JayesonLS/SmartWatchRedux/SmartWatchTest/SmartWatchTest.kicad_pcb

## KiCad design Schematic/RPN-Calculator/RPN-Calculator.sch

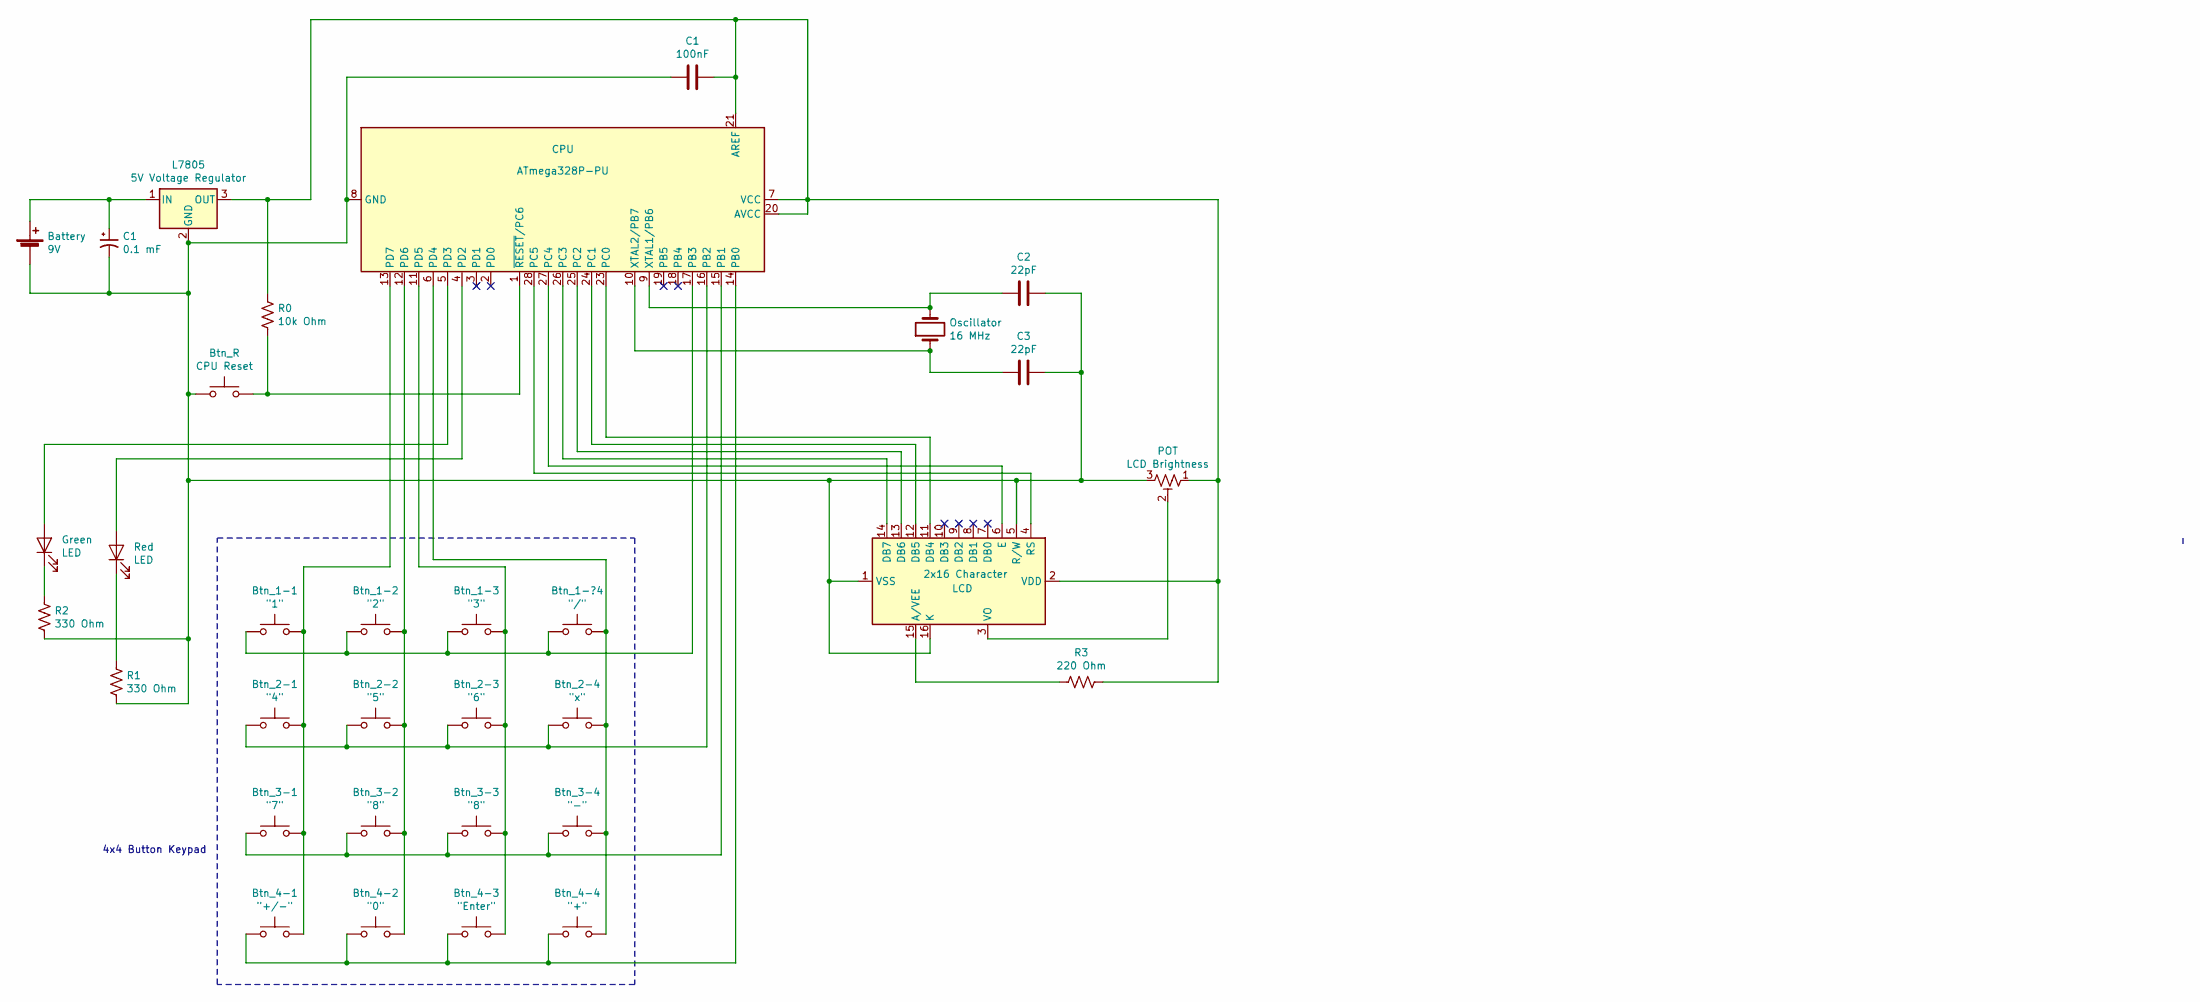
[picture p2: schematic RPN-Calculator.sch]

Parts:
Battery: 9V
Btn_1-1: \"1\"
Btn_1-2: \"2\"
Btn_1-3: \"3\"
Btn_1-?4: \"/\"
Btn_2-1: \"4\"
Btn_2-2: \"5\"
Btn_2-3: \"6\"
Btn_2-4: \"x\"
Btn_3-1: \"7\"
Btn_3-2, Btn_3-3: \"8\"
Btn_3-4: \"-\"
Btn_4-1: \"+/-\"
Btn_4-2: \"0\"
Btn_4-3: \"Enter\"
Btn_4-4: \"+\"
Btn_R: CPU Reset
C1: 100nF
C2, C3: 22pF
CPU: ATmega328P-PU; DIP-28_W7.62mm
Green: LED
L7805: 5V Voltage Regulator
LCD: 2x16 Character; RC1602A
Oscillator: 16 MHz
POT: LCD Brightness
R0: 10k Ohm
R1, R2: 330 Ohm
R3: 220 Ohm
Red: LED

Connections:
unnamed: Battery.1 (+), C1.1, L7805.1 (IN)
unnamed: Battery.2 (-), Btn_R.1, C1.2, C2.2, C3.2, CPU.8 (GND), CPU.22 (GND), L7805.2 (GND), LCD.1 (VSS), LCD.5 (R/W), LCD.16 (K), POT.3, R1.2, R2.2
unnamed: Btn_1-1.1, Btn_1-2.1, Btn_1-3.1, Btn_1-?4.1, CPU.17 (PB3)
unnamed: Btn_1-1.2, Btn_2-1.2, Btn_3-1.2, Btn_4-1.2, CPU.13 (PD7)
unnamed: Btn_1-2.2, Btn_2-2.2, Btn_3-2.2, Btn_4-2.2, CPU.12 (PD6)
unnamed: Btn_1-3.2, Btn_2-3.2, Btn_3-3.2, Btn_4-3.2, CPU.11 (PD5)
unnamed: Btn_1-?4.2, Btn_2-4.2, Btn_3-4.2, Btn_4-4.2, CPU.6 (PD4)
unnamed: Btn_2-1.1, Btn_2-2.1, Btn_2-3.1, Btn_2-4.1, CPU.16 (PB2)
unnamed: Btn_3-1.1, Btn_3-2.1, Btn_3-3.1, Btn_3-4.1, CPU.15 (PB1)
unnamed: Btn_4-1.1, Btn_4-2.1, Btn_4-3.1, Btn_4-4.1, CPU.14 (PB0)
unnamed: Btn_R.2, CPU.1 (~RESET~/PC6), R0.2
unnamed: C1.1, CPU.7 (VCC), CPU.20 (AVCC), CPU.21 (AREF), L7805.3 (OUT), LCD.2 (VDD), POT.1, R0.1, R3.1
unnamed: C2.1, CPU.9 (XTAL1/PB6), Oscillator.2
unnamed: C3.1, CPU.10 (XTAL2/PB7), Oscillator.1
unnamed: CPU.4 (PD2), Red.2 (A)
unnamed: CPU.5 (PD3), Green.2 (A)
unnamed: CPU.23 (PC0), LCD.11 (DB4)
unnamed: CPU.24 (PC1), LCD.12 (DB5)
unnamed: CPU.25 (PC2), LCD.13 (DB6)
unnamed: CPU.26 (PC3), LCD.14 (DB7)
unnamed: CPU.27 (PC4), LCD.6 (E)
unnamed: CPU.28 (PC5), LCD.4 (RS)
unnamed: Green.1 (K), R2.1
unnamed: LCD.3 (VO), POT.2
unnamed: LCD.15 (A/VEE), R3.2
unnamed: R1.1, Red.1 (K)

Notes on the sheet:
4x4 Button Keypad
